OLIMEX/SIMON-85/ARDUINO EXAMPLE/Simon/notes.h

/*

	Reference table with duration of some notes

    Copyright (C) 2014	Stefan Mavrodiev @ OLIMEX LTD

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
    You should have received a copy of the GNU General Public License
    along with this program.  If not, see <http://www.gnu.org/licenses/>.
*/
    
#ifndef __NOTES_H_
#define __NOTES_H_

#define A2 4545
#define Bb2 4290
#define B2 4049
#define C2 3822
#define Db2 3607
#define D2 3405
#define Eb2 3214
#define E2 3033
#define F2 2863
#define Gb2 2702
#define G2 2551
#define Ab2 2407

#define A3 2272
#define Bb3 2145
#define B3 2024
#define C3 1911
#define Db3 1803
#define D3 1702
#define Eb3 1607
#define E3 1516
#define F3 1431
#define Gb3 1351
#define G3 1275
#define Ab3 1203

#define A4 1136
#define Bb4 1072
#define B4 1012
#define C4 955
#define Db4 901
#define D4 851
#define Eb4 803
#define E4 758
#define F4 715
#define Gb4 675
#define G4 637
#define Ab4 601

#define A5 568
#define Bb5 536
#define B5 506
#define C5 477
#define Db5 450
#define D5 425
#define Eb5 401
#define E5 379
#define F5 357
#define Gb5 337
#define G5 318
#define Ab5 300

#define A6 284
#define Bb6 268
#define B6 253
#define C6 238
#define Db6 225
#define D6 212
#define Eb6 200
#define E6 189
#define F6 178
#define Gb6 168
#define G6 159
#define Ab6 150

#define REST 0

#endif
